jorgehsmp/EDUPI4.0/Transferencia/Imágenes/Carcasa (1).jpeg

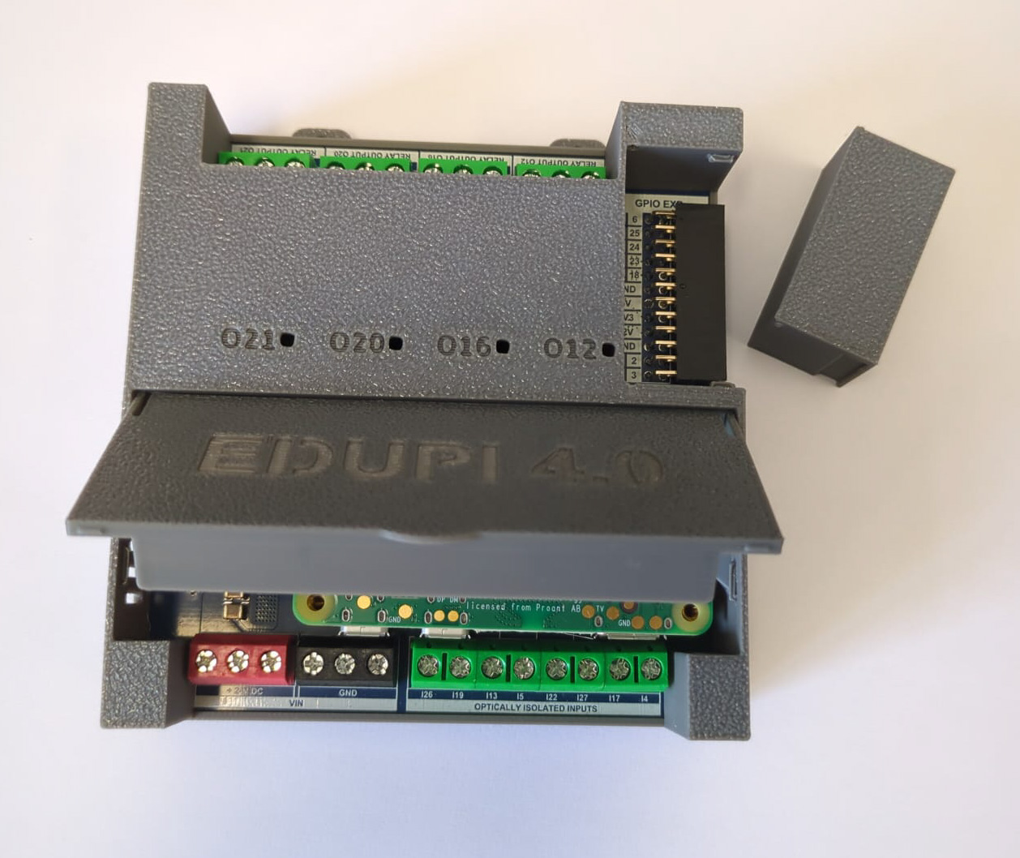
Transferencia/Imágenes/Carcasa (1).jpeg
