jorgehsmp/EDUPI4.0/Transferencia/Imágenes/Codesys.png

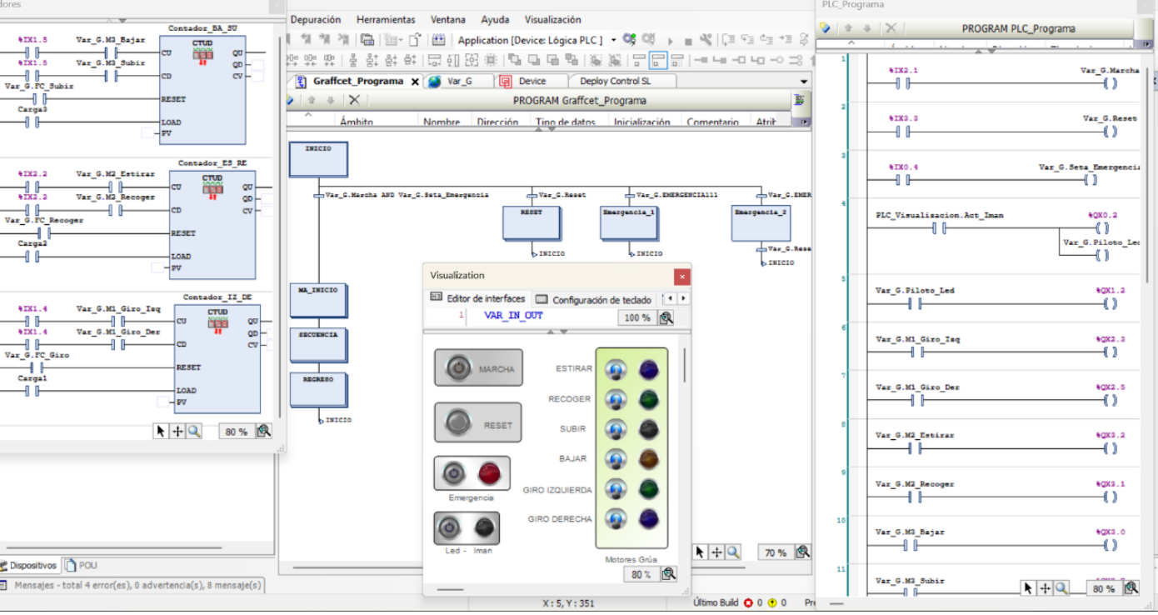
Transferencia/Imágenes/Codesys.png
