jorgehsmp/EDUPI4.0/Transferencia/Imágenes/Diagrama flujo hw-sw (1).png

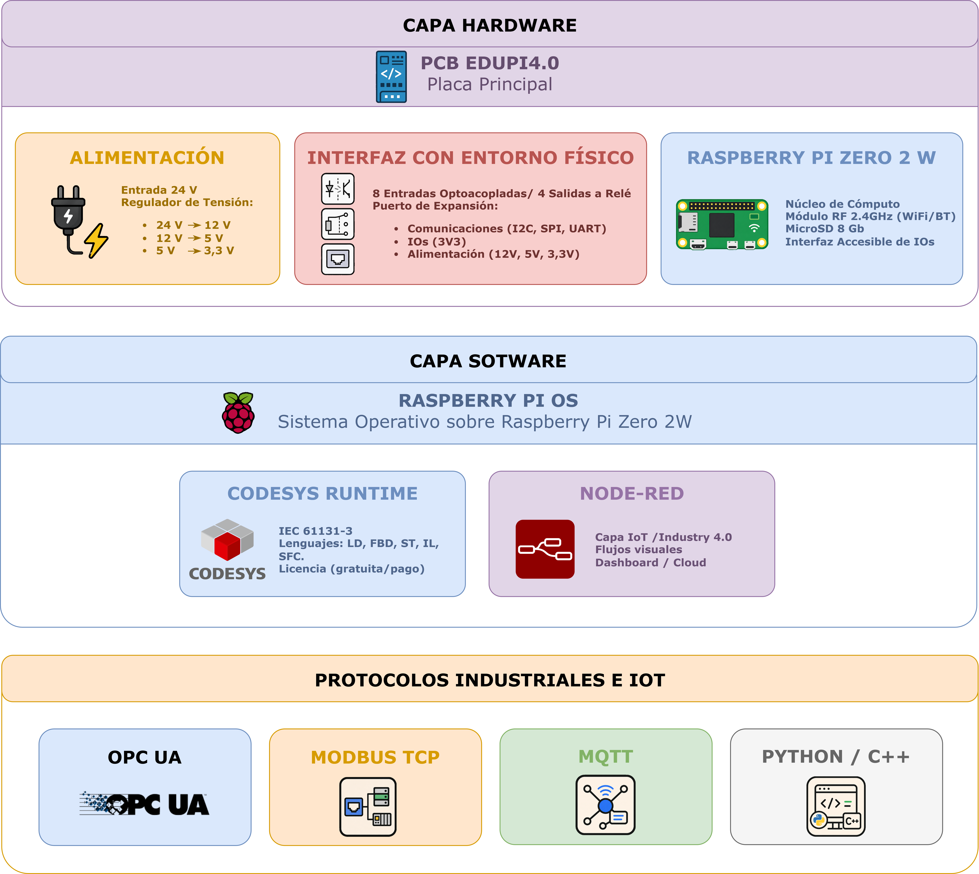
Transferencia/Imágenes/Diagrama flujo hw-sw (1).png
