jorgehsmp/EDUPI4.0/Transferencia/Imágenes/Entradas (1).png

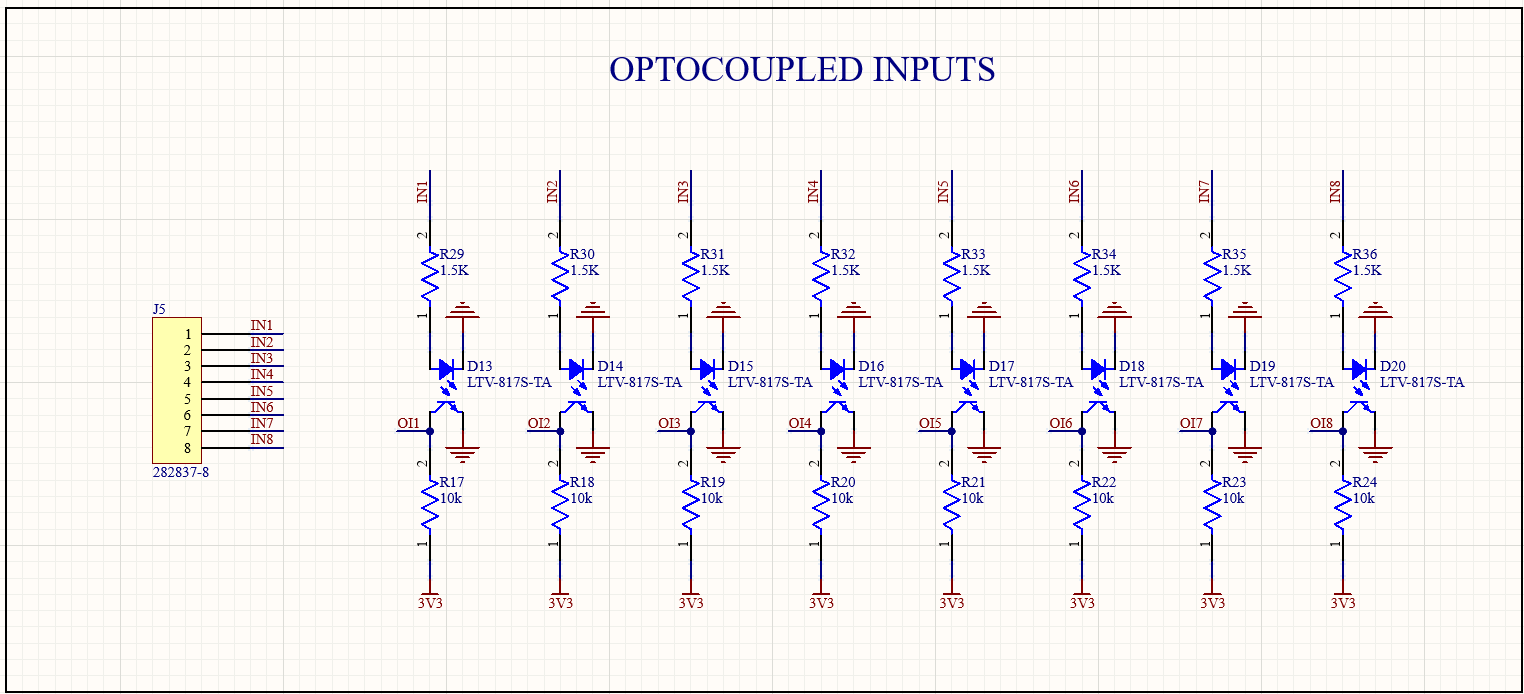
Transferencia/Imágenes/Entradas (1).png
