jorgehsmp/EDUPI4.0/Transferencia/Imágenes/Etapas de potencia (1).png

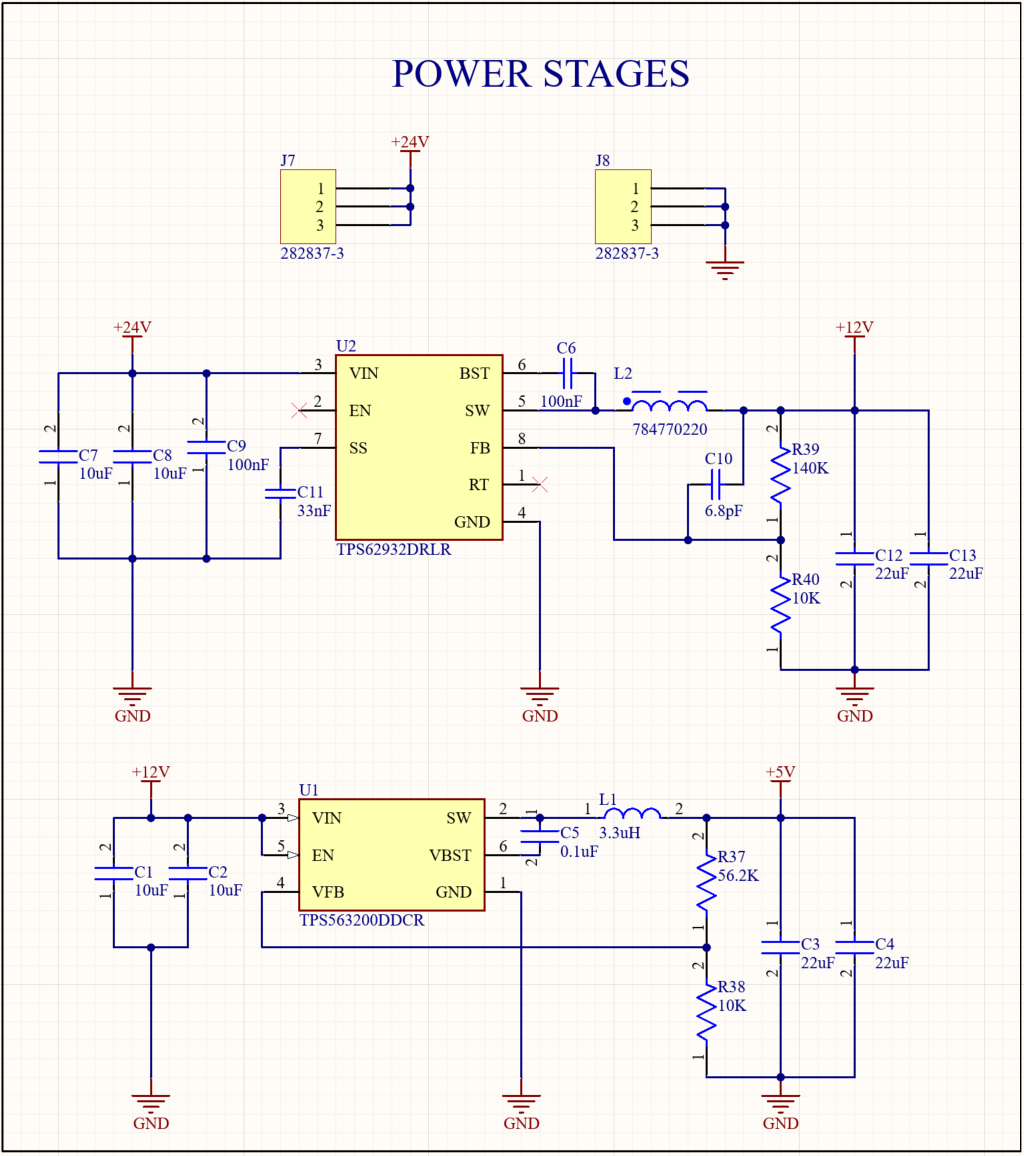
Transferencia/Imágenes/Etapas de potencia (1).png
