jorgehsmp/EDUPI4.0/Transferencia/Imágenes/Salida (1).png

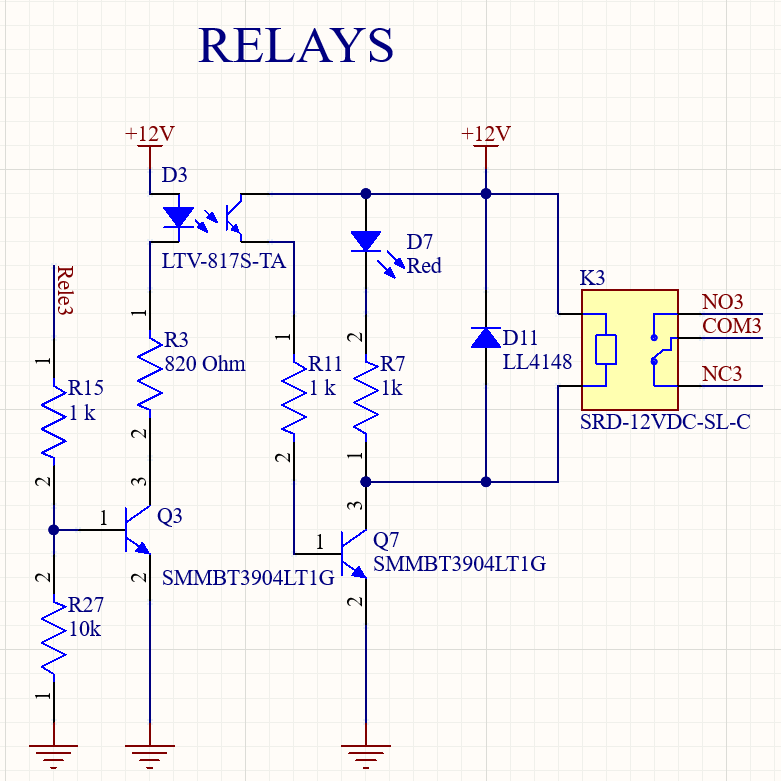
Transferencia/Imágenes/Salida (1).png
