jorgehsmp/EDUPI4.0/Transferencia/Imágenes/WhatsApp Image 2026-06-16 at 15.55.28.jpeg

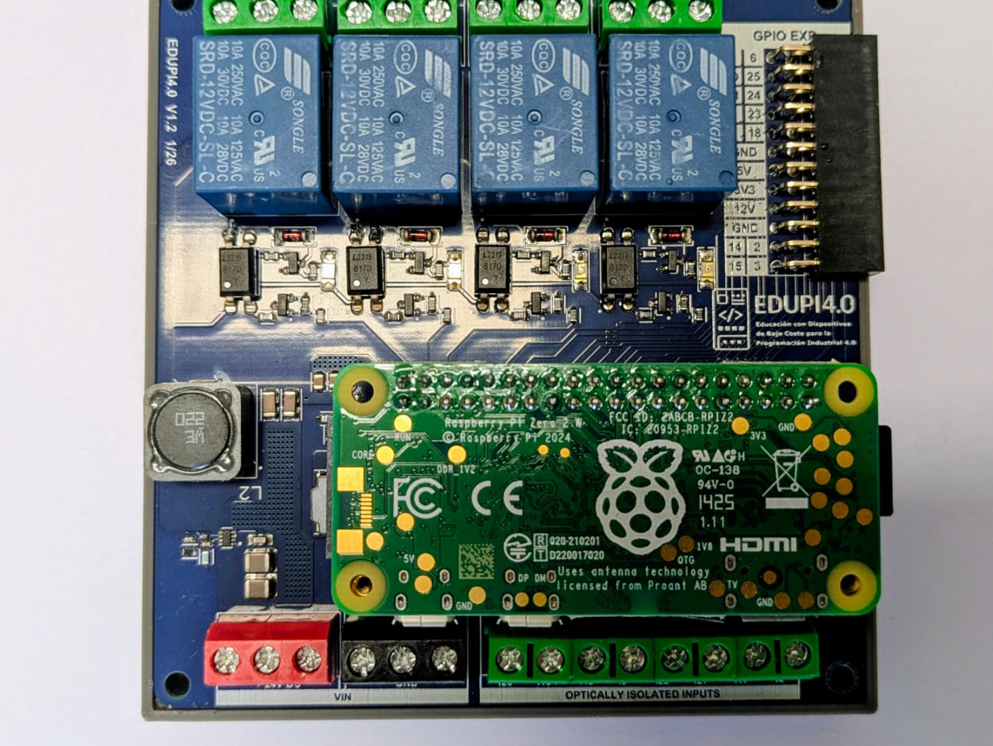
Transferencia/Imágenes/WhatsApp Image 2026-06-16 at 15.55.28.jpeg
