jorgehsmp/EDUPI4.0/Evaluación en aula/Imágenes montajes/bienCableadoPunteras.jpg

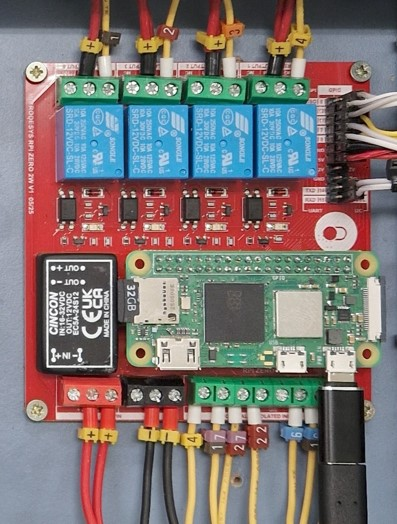
Evaluación en aula/Imágenes montajes/bienCableadoPunteras.jpg
