jorgehsmp/EDUPI4.0/Evaluación en aula/Imágenes montajes/SantiMidiendo.jpg

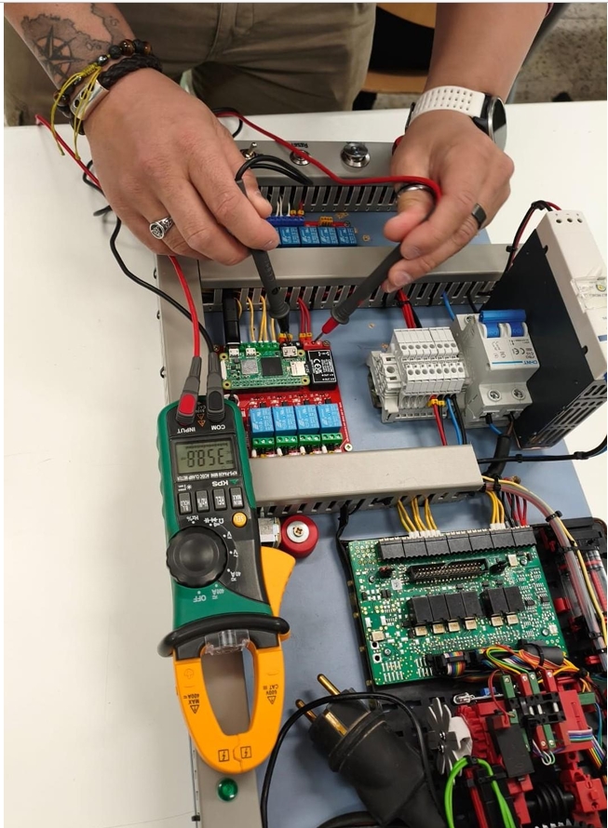
Evaluación en aula/Imágenes montajes/SantiMidiendo.jpg
