jorgehsmp/EDUPI4.0/Evaluación en aula/Imágenes montajes/Screenshot_1.png

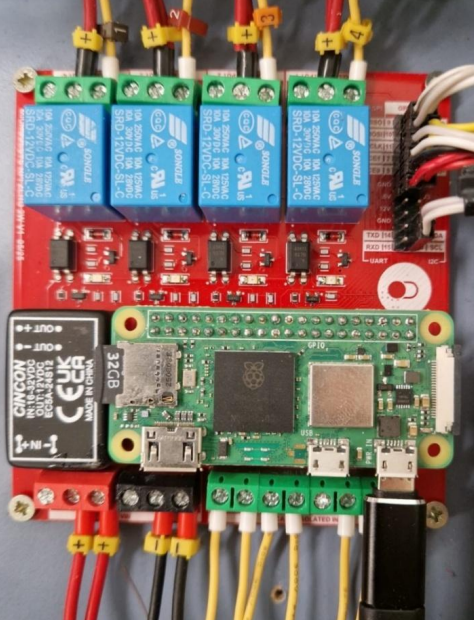
Evaluación en aula/Imágenes montajes/Screenshot_1.png
