jorgehsmp/EDUPI4.0/Evaluación en aula/Imágenes montajes/Screenshot_2.png

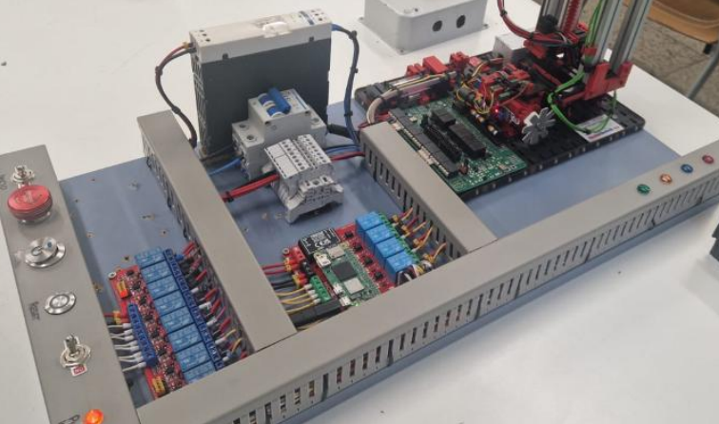
Evaluación en aula/Imágenes montajes/Screenshot_2.png
