jorgehsmp/EDUPI4.0/Evaluación en aula/Imágenes montajes/Screenshot_4.png

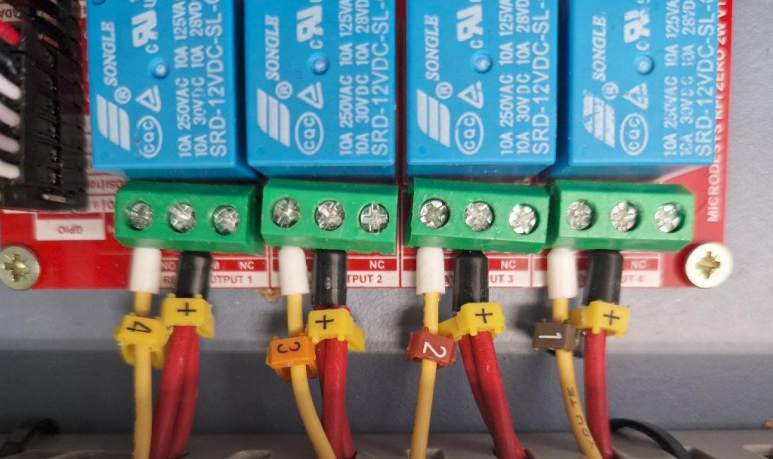
Evaluación en aula/Imágenes montajes/Screenshot_4.png
