jorgehsmp/EDUPI4.0/Evaluación en aula/Imágenes montajes/Screenshot_7.png

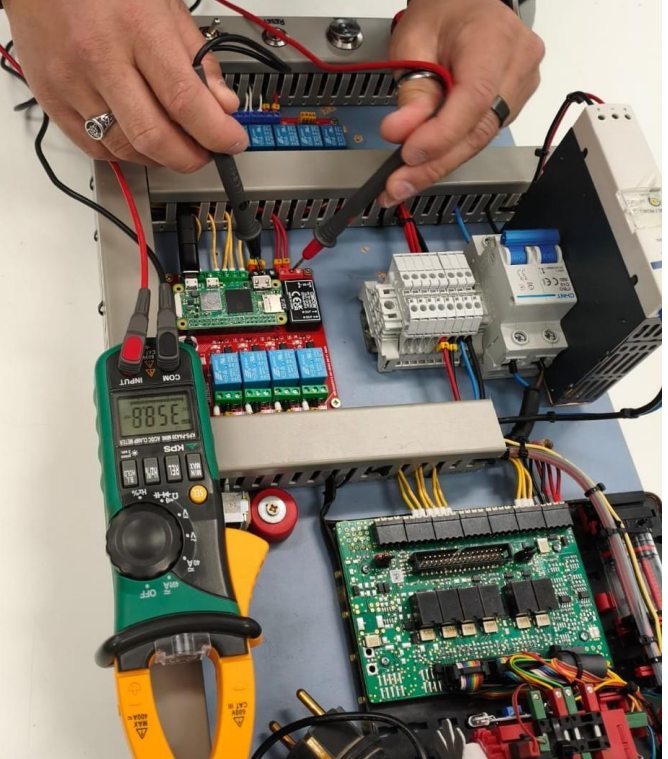
Evaluación en aula/Imágenes montajes/Screenshot_7.png
