jorgehsmp/EDUPI4.0/Evaluación en aula/Imágenes montajes/Screenshot_10.png

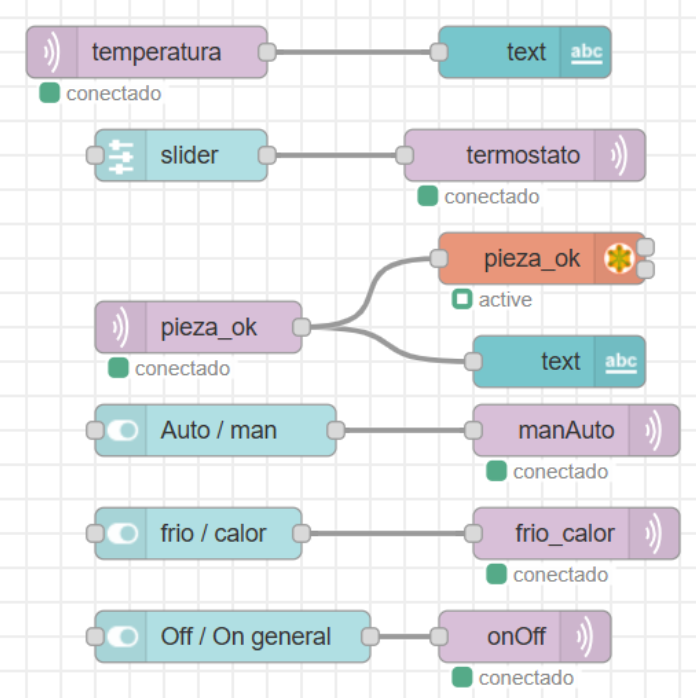
Evaluación en aula/Imágenes montajes/Screenshot_10.png
