jorgehsmp/EDUPI4.0/Evaluación en aula/Imágenes montajes/Screenshot_11.png

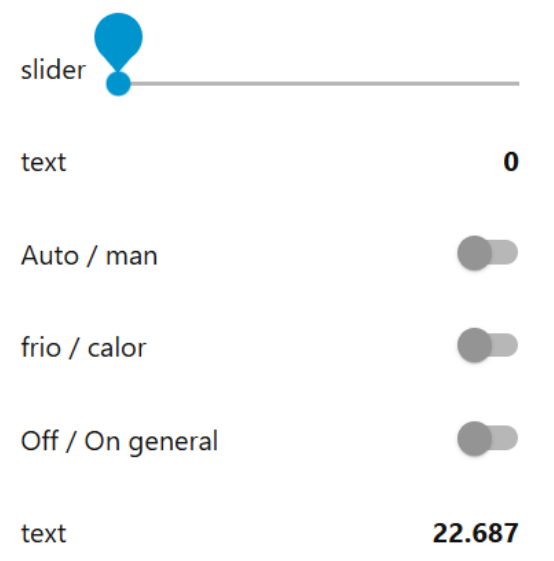
Evaluación en aula/Imágenes montajes/Screenshot_11.png
