jorgehsmp/EDUPI4.0/Evaluación en aula/Imágenes montajes/WhatsApp Image 2026-06-16 at 11.55.54 (1).jpeg

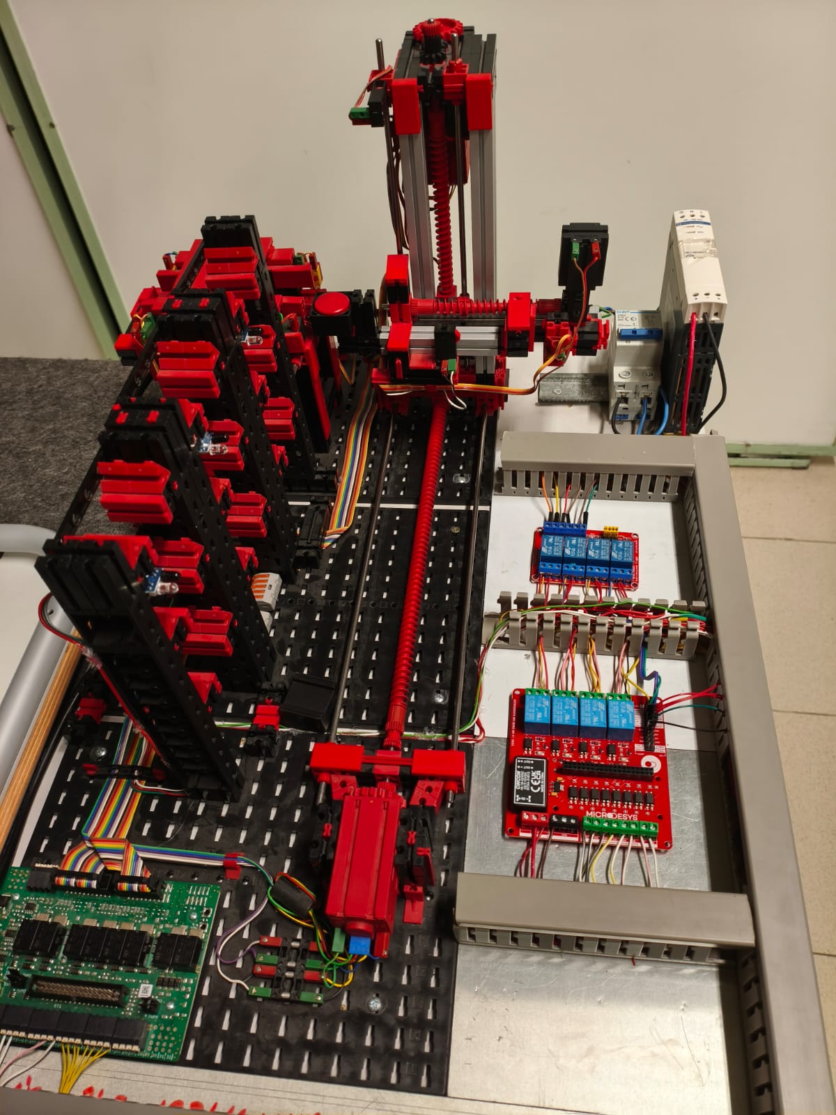
Evaluación en aula/Imágenes montajes/WhatsApp Image 2026-06-16 at 11.55.54 (1).jpeg
